teensytheremin/theremin/schematics/ltspice/2023_03_bjt_dual_ota_current_sensing_oscillator_v01.asc

C1: cap; 10pF
C_ant: cap; 8pF
C_hand: cap; 0.0001pF
L1: ind; 2.7mH; Ipk=0.5 Rser=120 Cpar=1.1pF
Q1: npn; 2N3904
Q2: npn; 2N3904
Q3: pnp; 2N3906
Q4: pnp; 2N3906
Q5: npn; 2N3904
Q6: npn; 2N3904
Q7: pnp; 2N3906
Q8: pnp; 2N3906
Q9: npn; 2N3904
Q10: npn; 2N3904
Q11: npn; 2N3904
Q12: npn; 2N3904
R1: res; 180
R2: res; 220
R3: res; 15
R4: res; 2k
R5: res; 47
R6: res; 1
R7: res; 1
R8: res; 100
R9: res; 1.5k
R10: res; 47
R11: res; 1
R_loss: res; 10Meg
V1: voltage; 3.3
Named nets: 0, COM, ANT, DRIVE, SENSE
.tran 0 1000u 10u 1n uic
Current Sensing OTA Based Theremin Oscillator
.ic I(L1)=0.0001
