teensytheremin/theremin/schematics/ltspice/2023_04_bjt_trans_cond_mixer_with_volume_vca_v01.asc

C1: cap; 2.2µF
C2: cap; 1nF
C3: cap; 1nF
C4: cap; 1nF
C5: cap; 360nF
C8: cap; 10nF
Q1: npn; 2N3904
Q2: npn; 2N3904
Q3: npn; 2N3904
Q4: npn; 2N3904
Q5: pnp; 2N3906
Q6: pnp; 2N3906
Q7: npn; 2N3904
Q8: npn; 2N3904
Q9: npn; 2N3904
Q10: npn; 2N3904
Q11: npn; 2N3904
Q12: pnp; 2N3906
Q13: pnp; 2N3906
Q14: npn; 2N3904
R1: res; 220
R2: res; 220
R3: res; 10k
R4: res; 10k
R5: res; 10k
R6: res; 15k
R7: res; 10k
R8: res; 10k
R9: res; 220
R10: res; 470
R11: res; 470
R12: res; 470
R15: res; 2.2k
R16: res; 2.2k
V1: voltage; 3.3
V2: voltage; SINE(1.65 0.5 1000000)
V3: voltage; SINE(1.65 0.8 10)
V5: voltage; SINE(1.65 0.5 1001000)
Named nets: 0, COM, IN1, IN2, OUT, VCTL
.tran 0 307m 3m uic
High Quality Operational Transconductance Amplifier based Theremin Mixer with volume control
1 Vpp
1 Vpp
1 Vpp
Volume voltage control (<0.1.1V to mute)
