teensytheremin/theremin/schematics/ltspice/2023_03_bjt_trans_cond_mixer_v01.asc

C1: cap; 360nF
C2: cap; 1nF
C3: cap; 1nF
C4: cap; 1nF
Q1: npn; 2N3904
Q2: npn; 2N3904
Q3: npn; 2N3904
Q4: npn; 2N3904
Q5: pnp; 2N3906
Q6: pnp; 2N3906
Q7: npn; 2N3904
R1: res; 2.2k
R2: res; 2.2k
R3: res; 10k
R4: res; 10k
R5: res; 10k
R6: res; 15k
R7: res; 10k
R8: res; 10k
R9: res; 220
V1: voltage; 3.3
V2: voltage; SINE(1.65 0.5 1000000)
V5: voltage; SINE(1.65 0.5 1001000)
Named nets: 0, COM, OUT, IN1, IN2
.tran 0 7m 3m uic
High Quality Operational Transconductance Amplifier based Theremin Mixer
1 Vpp
1 Vpp
1 Vpp
