teensytheremin/theremin/schematics/ltspice/2023_03_bjt_trans_cond_volt_follower_current_sensing_buffer_v01.asc

C_ant: cap; 8pF
C_hand: cap; 0.0001pF
I1: current; 6mA
L1: ind; 2.7mH; Ipk=0.5 Rser=120 Cpar=1.1pF
Q1: npn; 2N3904
Q2: npn; 2N3904
Q3: npn; 2N3904
Q4: npn; 2N3904
Q5: npn; 2N3904
Q6: npn; 2N3904
Q7: pnp; 2N3906
Q8: pnp; 2N3906
Q9: npn; 2N3904
Q10: pnp; 2N3906
Q11: pnp; 2N3906
Q12: pnp; 2N3906
R1: res; 470
R2: res; 470
R3: res; 1
R4: res; 1
R5: res; 1
R6: res; 1
R7: res; 1
R8: res; 1
R9: res; 1
R10: res; 1
R11: res; 1.1
R12: res; 1
R_loss: res; 10Meg
V1: voltage; 3.3
V2: voltage; SINE(1.65 0.75 1014288)
Named nets: 0, COM, ANT, DRIVE, SENSE, DRV_IN
.tran 0 230u 200u 1n uic
Current Sensing Theremin 
Analog Frontend
.ic V(ANT)=0.00001
