teensytheremin/theremin/schematics/ltspice/2023_03_bjt_diff_amp_volt_follower_buffer_v01.asc

C_ant: cap; 8pF
C_hand: cap; 0.0001pF
L1: ind; 2.7mH; Ipk=0.5 Rser=120 Cpar=1.1pF
Q1: npn; 2N3904
Q2: npn; 2N3904
Q3: pnp; 2N3906
Q4: pnp; 2N3906
Q5: npn; 2N3904
Q6: npn; 2N3904
Q7: npn; 2N3904
Q8: npn; 2N3904
Q9: npn; 2N3904
R1: res; 22
R2: res; 470
R3: res; 470
R_loss: res; 10Meg
V1: voltage; 3.3
V2: voltage; SINE(1.55 0.85 1014288)
Named nets: 0, COM, ANT, DRIVE, SENSE, DRV_IN
.tran 0 2m 1u 1n uic
Current Sensing Theremin Oscillator
.ic V(ANT)=0.0001
