teensytheremin/theremin/schematics/ltspice/2023_03_wallin_oscillator_bjt_diff_amp_volt_follower_buffer_v01.asc

C11: cap; 2nF
C12: cap; 2nF
C13: cap; 2nF
C_ant: cap; 8pF
C_hand: cap; 0.0001pF
L1: ind; 2.7mH; Ipk=0.5 Rser=120 Cpar=1.1pF
Q11: npn; 2N3904
Q12: npn; 2N3904
Q13: npn; 2N3904
Q15: pnp; 2N3906
Q16: pnp; 2N3906
Q17: npn; 2N3904
Q18: npn; 2N3904
Q19: npn; 2N3904
Q20: npn; 2N3904
Q21: npn; 2N3904
Q22: npn; 2N3904
Q23: npn; 2N3904
Q24: npn; 2N3904
Q25: npn; 2N3904
Q26: npn; 2N3904
Q28: npn; 2N3904
Q29: npn; 2N3904
R3: res; 270k
R7: res; 470
R20: res; 270k
R23: res; 47
R24: res; 510
R25: res; 2k
R29: res; 22
R37: res; 330
R_loss: res; 10Meg
V1: voltage; 3.3
Named nets: 0, COM, ANT, DRIVE, SENSE, SENSE_BUF, DRV_IN, AMP_OUT
.tran 0 2m 1u 1n uic
Current Sensing Theremin Oscillator
.ic V(ANT)=0.0001
