teensytheremin/theremin/schematics/ltspice/2023_03_wallin_oscillator_bjt_power_rails_diff_amp_4bjt_buffer_v01.asc

C1: cap; 1nF
C2: cap; 1nF
C3: cap; 1nF
C4: cap; 1nF
C5: cap; 0.1µF
C6: cap; 0.1µF
C7: cap; 10nF
C8: cap; 0.1µF
C_ant: cap; 8pF
C_hand: cap; 0.0001pF
L1: ind; 2.7mH; Ipk=0.5 Rser=120 Cpar=1.1pF
Q1: npn; 2N3904
Q2: npn; 2N3904
Q3: npn; 2N3904
Q4: npn; 2N3904
Q5: pnp; 2N3906
Q6: pnp; 2N3906
Q7: pnp; 2N3906
Q8: npn; 2N3904
Q9: npn; 2N3904
Q10: pnp; 2N3906
R1: res; 47
R2: res; 47
R3: res; 270
R4: res; 200
R5: res; 200
R6: res; 470
R7: res; 470
R8: res; 15k
R9: res; 15k
R10: res; 1.5k
R11: res; 1k
R_loss: res; 10Meg
V1: voltage; 3.3
Named nets: 0, COM, ANT, Vbias, DRIVE, DOUT, DIN
.tran 0 2m 1u 1n uic
Current Sensing Theremin Oscillator
.ic V(ANT)=0.0001
