teensytheremin/theremin/schematics/ltspice/2023_03_wallin_oscillator_bjt_power_rails_diff_amp_with_current_mirror_v01.asc

C1: cap; 1nF
C2: cap; 1nF
C3: cap; 1nF
C4: cap; 1nF
C5: cap; 0.1µF
C6: cap; 0.1µF
C_ant: cap; 8pF
C_hand: cap; 0.0001pF
L1: ind; 2.7mH; Ipk=0.5 Rser=120 Cpar=1.1pF
Q1: npn; 2N3904
Q2: npn; 2N3904
Q3: npn; 2N3904
Q4: npn; 2N3904
Q5: pnp; 2N3906
Q6: pnp; 2N3906
R1: res; 22
R2: res; 22
R3: res; 22
R4: res; 47
R5: res; 360
R6: res; 24k
R7: res; 24k
R8: res; 1k
R9: res; 1k
R_loss: res; 10Meg
V1: voltage; 3.3
Named nets: 0, COM, ANT
.tran 0 1m 10u 1n uic
Current Sensing Theremin Oscillator
.ic V(ANT)=0.0001
