teensytheremin/theremin/schematics/ltspice/2023_03_wallin_oscillator_bjt_power_rails_diff_amp_v01.asc

C1: cap; 1nF
C2: cap; 1nF
C3: cap; 1nF
C4: cap; 1nF
C5: cap; 0.1µF
C6: cap; 0.1µF
C_ant: cap; 8pF
C_hand: cap; 0.0001pF
L1: ind; 2.7mH; Ipk=0.5 Rser=120 Cpar=1.1pF
Q1: npn; 2N3904
Q2: npn; 2N3904
Q3: npn; 2N3904
Q4: npn; 2N3904
Q5: pnp; 2N3906
Q6: npn; 2N3904
Q7: npn; 2N3904
Q8: pnp; 2N3906
Q10: npn; 2N3904
Q11: npn; 2N3904
R1: res; 33
R2: res; 33
R3: res; 1.2k
R4: res; 860
R5: res; 860
R6: res; 1.5k
R7: res; 1k
R8: res; 1k
R9: res; 1k
R10: res; 47k
R11: res; 47k
R_loss: res; 10Meg
V1: voltage; 3.3
Named nets: 0, COM, ANT, Vbias, VP, VN, DRIVE
.tran 0 2m 10u 1n uic
Current Sensing Theremin Oscillator
.ic V(ANT)=0.0001
