teensytheremin/theremin/schematics/ltspice/2023_02_sine_drive_phase_shift.asc

C2: cap; 100nF
C_ant: cap; 8pF
C_hand: cap; 0.001pF
L1: ind; 2.7mH; Ipk=0.5 Rser=120 Cpar=1.1pF
R1: res; 8.2K
R2: res; 2.2K
R3: res; 22
R7: res; 10K
R_loss: res; 100Meg
U2: adcmp601
U3: adcmp601
U4: ad8651
V1: voltage; 3.3V
V2: voltage; SINE(0.344 0.306 1015.288KHz)
Named nets: 0, COM, DRV065, DRIVE, ANT, SENSE, REF
.tran 0 500u 100u
Air core inductor
Theremin sensor analog frontend
AD9833 sin out
