teensytheremin/theremin/schematics/ltspice/2021_current_sensing_unbuffered_inverters_06.asc

C1: cap; 0.1µF
C2: cap; 47pF
C3: cap; 47pF
C4: cap; 47pF
C_ant: cap; 10pF
L2: ind; 2700µH; Rser=120 Cpar=1.2pF
Q1: pnp; BC857B
Q2: pnp; BC857B
Q3: npn; BC847B
Q4: npn; BC847B
R1: res; 2.2
R2: res; 2.2
R3: res; 10
R4: res; 10
R5: res; 1.5k
R6: res; 1.5k
R7: res; 1.5k
R8: res; 100k
R9: res; 100k
R10: res; 100k
U1: 74LVCU04NXP
U2: 74LVCU04NXP
U3: 74LVCU04NXP
U4: 74LVCU04NXP
V2: voltage; 3.3V
Named nets: 0, COM, SENSE2, ANT, DRIVE, OUT2, SENSE1
.tran 0 5m 0.001u 0.3n
Theremin sensor - current sensing oscillator on 74LVC2GU04 unbuffered inverters and BJT current mirrors
.ic I(L1)=0.001u
Current sensor
Preamp
Driver
Output buffer
