teensytheremin/theremin/schematics/ltspice/2021_current_sensing_unbuffered_inverters_05.asc

C1: cap; 220pF
C2: cap; 220pF
C3: cap; 1µF
C_ant: cap; 10pF
L1: ind; 2700µH; Rser=120 Cpar=1.2pF
R1: res; 10
R2: res; 10
R3: res; 1k
R4: res; 1k
R5: res; 100k
R6: res; 100k
R7: res; 100k
U1: 74LVCU04NXP
U2: 74LVCU04NXP
U3: 74LVCU04NXP
U4: 74LVCU04NXP
V2: voltage; 3.3V
Named nets: 0, COM, ANT, DRIVE, SENSE, OUT, TOPV, BOTTOMV
.tran 0 5m 0.001u 0.3n
Current sensing oscillator on unbuffered inverters
.ic I(L1)=0.001u
