teensytheremin/theremin/schematics/ltspice/2021_current_sensing_unbuffered_inverters_03.asc

C1: cap; 200pF
C2: cap; 200pF
C3: cap; 0.1µF
C_ant: cap; 10pF
L1: ind; 2700µH; Rser=120 Cpar=1.2pF
R1: res; 10
R2: res; 10
R3: res; 100k
R4: res; 100k
U1: 74HCU04X
U2: 74HCU04X
U3: 74HCU04X
U4: 74HCU04X
U5: 74HCU04X
U6: 74HCU04X
V2: voltage; 3.3V
Named nets: 0, COM, ANT, DRIVE, OUT
.tran 0 5m 0.001u 0.1n
Current sensing oscillator on unbuffered inverters
.ic I(L1)=0.001u
