teensytheremin/theremin/schematics/ltspice/2021_current_sensing_unbuffered_inverters_01.asc

C1: cap; 0.1µF
C6: cap; 0.01µF
C_ant1: cap; 8pF
C_ant: cap; 8pF
L1: ind; 2700µH; Rser=120 Cpar=1.2pF
L2: ind; 2700µH; Rser=120 Cpar=1.2pF
R1: res; 1
R2: res; 1
R3: res; 47
R4: res; 220
R5: res; 220
R6: res; 1
R7: res; 22
R8: res; 22
R9: res; 1
R10: res; 15
R11: res; 15
R12: res; 1
R13: res; 47
R14: res; 1000
R15: res; 1045
R16: res; 1
R17: res; 1000k
R19: res; 1000k
U1: SN74LVC2GU04
U2: SN74LVC2GU04
U3: 74HCU04X
U4: SN74LVC2GU04
U5: SN74LVC2GU04
U6: 74HCU04X
U7: 74HCU04X
U8: 74HCU04X
V2: voltage; 3.3V
Named nets: 0, COM, ANT, DRIVE, OUT, ANT2, DRIVE2, OUT2
.tran 0 5m 0.001u 0.1n
.ic I(L1)=0.001u
.ic I(L2)=0.01u
Current sensing oscillator on unbuffered inverters
