teensytheremin/theremin/schematics/ltspice/2021_current_sensing_pll_bjts_01.asc

C1: cap; 1µF
C2: cap; 1µF
C3: cap; 1µF
C4: cap; 1µF
C5: cap; 1µF
C6: cap; 1µF
C7: cap; 470pF
C8: cap; 0.1µF
C9: cap; 100pF
C11: cap; 0.1µF
C_ant: cap; 10pF
C_vco: cap; 160pF
L1: ind; 2700µH; Rser=120 Cpar=1.2pF
L2: ind; 100µH; Rser=120 Cpar=1.2pF
Q1: pnp; 2N3906
Q2: npn; 2N3904
Q3: pnp; 2N3906
Q4: npn; 2N3904
Q5: pnp; 2N3906
Q6: npn; 2N3904
Q7: npn; 2N3904
Q8: pnp; 2N3906
Q9: npn; 2N3904
Q10: pnp; 2N3906
Q11: npn; 2N3904
Q12: pnp; 2N3906
Q13: npn; 2N3904
Q14: pnp; 2N3906
Q15: npn; 2N3904
Q16: pnp; 2N3906
Q17: npn; 2N3904
Q18: pnp; 2N3906
Q19: npn; 2N3904
Q20: pnp; 2N3906
R1: res; 2.2k
R2: res; 2.2k
R3: res; 2
R4: res; 2
R5: res; 1k
R6: res; 1k
R7: res; 10
R8: res; 10
R9: res; 1k
R10: res; 4.7k
R11: res; 470
R12: res; 4.7k
R13: res; 470
R14: res; 10
R15: res; 10
R16: res; 10k
R17: res; 10k
R18: res; 4.7k
R19: res; 220
R20: res; 10k
R23: res; 330
R24: res; 1500
R25: res; 4.7k
R27: res; 4.7k
R28: res; 4.7k
U1: BBY65-02V
U2: BBY65-02V
U3: 74lvc86a
U4: SN74LVC1GX04
U5: SN74LVC1GX04
V2: voltage; 3.3V
Named nets: 0, COM, ANT, DRIVE, DRIVE_IN, VCOINDOUT, VCODRIVE, OUT, SENSE, VCO90, VCOCTL
.tran 0 5m 0.001u 1n
.ic I(L2)=0.0001u
integrator
VCO current sensing
drive current sensing
VCO tank
drive
VCO drive
antenna tank
phase detector
Current Sensing PLL Theremin Oscillator
phase correction
