teensytheremin/theremin/schematics/ltspice/2021_current_sensing_8bjts_01.asc

C1: cap; 1µF
C2: cap; 1µF
C3: cap; 1µF
C_ant: cap; 8pF
D1: diode
D2: diode
L1: ind; 2700µH; Rser=120 Cpar=1.2pF
Q1: pnp; 2N3906
Q2: npn; 2N3904
Q3: pnp; 2N3906
Q4: npn; 2N3904
Q5: pnp; 2N3906
Q6: npn; 2N3904
Q7: npn; 2N3904
Q8: pnp; 2N3906
R1: res; 470
R2: res; 470
R3: res; 2.2
R4: res; 2.2
R5: res; 1k
R6: res; 1k
R7: res; 15
R8: res; 15
R9: res; 470
V2: voltage; 3.3V
Named nets: 0, COM, ANT, DRIVE, SENSE_OUT
.tran 0 5m 0.001u 1n
.ic I(L1)=0.001u
