teensytheremin/theremin/schematics/ltspice/2021_current_sensing_opamps_pll_01.asc

C1: cap; 0.1µ
C2: cap; 0.1µ
C3: cap; 120pF
C4: cap; 220pF
C5: cap; 0.01µ
C6: cap; 330pF
C7: cap; 0.33µ
C8: cap; 33pF
C_ant1: cap; 10pF
L1: ind; 200µH; Rser=3 Cpar=1.2pF
L2: ind; 2700µH; Rser=120 Cpar=1.2pF
R1: res; 220
R2: res; 2.7k
R3: res; 220
R4: res; 2.7k
R5: res; 220
R6: res; 100
R7: res; 220
R8: res; 1k
R9: res; 1.1k
R10: res; 2.2k
R11: res; 1k
R12: res; 3.3k
R13: res; 22k
R14: res; 33k
R15: res; 47
R16: res; 1000
R17: res; 22k
R20: res; 1k
R21: res; 1k
R_sense: res; 10
U1: ad8132
U2: ADA4807-1
U3: adcmp601
U4: 74lvc86a
U6: SN74LVC1GX04
U7: SN74LVC1GX04
U8: AD8541
U100: BBY65-02V
U101: BBY65-02V
V2: voltage; 3.3V
Named nets: 0, COM, VCOINDOUT, VCOINDIN, VCODRIVE, ANT, IND_IN, OUT, DRIVE, VCOCTL
.tran 0 5m 0.001u 5n
.ic I(L1)=0.001u
