teensytheremin/theremin/schematics/ltspice/2021_current_sensing_dual_opamps_01.asc

C2: cap; 330pF
C4: cap; 0.1µ
C_ant: cap; 10pF
L1: ind; 2700µH; Rser=120 Cpar=1.2pF
R1: res; 22k
R4: res; 2.4k
R5: res; 2.4k
R6: res; 110
R7: res; 110
R8: res; 10k
R9: res; 10
R10: res; 1k
R11: res; 3k
U1: ad8132
U2: ADA4807-1
V2: voltage; 3.3V
Named nets: 0, COM, ANT, TANK_IN, DRIVE, DIFF
.tran 0 5m 0.001u 1n
.ic I(L1)=0.001u
