teensytheremin/theremin/schematics/ltspice/2021_current_sensing_unbuffered_inverter_01.asc

C1: cap; 0.1µF
C2: cap; 0.1µF
C3: cap; 0.1µF
C_ant1: cap; 8pF
C_ant2: cap; 8pF
L1: ind; 2700µH; Rser=120 Cpar=1.2pF
L2: ind; 2700µH; Rser=120 Cpar=1.2pF
Q1: npn; 2N3904
Q2: npn; 2N3904
Q3: pnp; 2N3906
Q4: pnp; 2N3906
R1: res; 10
R2: res; 10
R3: res; 470
R4: res; 470
R5: res; 10
R6: res; 10
R7: res; 470
R8: res; 470
R9: res; 2.2k
R10: res; 2.2k
R11: res; 10
R12: res; 10
U3: SN74LVC2GU04
U4: SN74LVC2GU04
U5: SN74LVC2GU04
U6: SN74LVC2GU04
V2: voltage; 3.3V
Named nets: 0, COM, ANT1, ANT2, DRIVE2, DRIVE1
.tran 0 5m 0.001m 0.0001u
.ic I(L1)=0.001u
.ic I(L2)=0.001u
