teensytheremin/theremin/schematics/ltspice/2021_current_sensing_oscillator_lt6200_01.asc

C1: cap; 0.5pF
C2: cap; 0.5pF
C3: cap; 0.1µF
C_ant: cap; 8pF
C_touch: cap; 330pF
D1: diode; BAS216
D2: diode; BAS216
D3: diode
D4: diode
D23: diode; BAS216
D24: diode; BAS216
L1: ind; 2.7mH; Rser=120 Cpar=1.2pF
Q29: npn; 2N3904
Q30: npn; 2N3904
R1: res; 220
R2: res; 220
R3: res; 2200
R4: res; 2200
R5: res; 220
R6: res; 220
R39: res; 10
R42: res; 100
R_sense: res; 22
R_touch: res; 150k
U1: LT6200-10
U2: ad8651
V2: voltage; 3.3V
Named nets: 0, COM, ANT, DRIVE, OUT
.tran 0 5m 0.001m 0.001u
.ic I(L1)=0.0001u
output buffer
ESD protection diodes
Current sensing Theremin oscillator
touch simulation
Limiter
