teensytheremin/theremin/schematics/ltspice/2021_current_sensing_current_mirrors_oscillator_05.asc

C1: cap; 10pF
C2: cap; 10pF
C11: cap; 10pF
D1: diode
D2: diode
D3: diode
D4: diode
L1: ind; 2.7mH; Rser=120 Cpar=1.2pF
L2: ind; 2.7mH; Rser=120 Cpar=1.2pF
L3: ind; 2.7mH; Rser=120 Cpar=1.2pF
Q1: pnp; 2N3906
Q2: pnp; 2N3906
Q3: npn; 2N3904
Q4: npn; 2N3904
Q5: pnp; 2N3906
Q6: pnp; 2N3906
Q7: npn; 2N3904
Q8: npn; 2N3904
Q9: pnp; 2N3906
Q10: npn; 2N3904
Q11: npn; 2N3904
Q12: pnp; 2N3906
R1: res; 3.3k
R2: res; 3.3k
R3: res; 33
R4: res; 33
R5: res; 2200
R6: res; 1000
R7: res; 1000
R8: res; 10
R9: res; 10
R10: res; 10
R11: res; 10
U3: ad8651
V1: voltage; SINE(1.65 1.65 915229)
V2: voltage; 3.3V
V3: voltage; 1.65
V4: voltage; PULSE(0 3.3 0 0.03u 0.03u 0.516311u 1.092623u)
Named nets: 0, COM, VREF, SIN_IN, SQ_IN, ANT, DRIVE, OPAMPOUT
.tran 0 5m 0.001m 0.001u
#.TRAN 1m
#.IC I(L)=6.188u
.IC I(L)=6.19u
.MEAS TRAN t1 V(Vant) WHEN V(Vant) = 0 rise=1
.MEAS TRAN t2 V(Vant) WHEN V(Vant) = 0 rise=2
.MEAS TRAN freq21 PARAM 1/(t2-t1)
.ic I(L3)=0.0001u
