teensytheremin/theremin/schematics/ltspice/2021_pll_current_sensing_04.asc

C1: cap; 100nF
C2: cap; 0.1µF
C3: cap; 1µF
C4: cap; 0.1µF
C5: cap; 0.1µF
C6: cap; 220pF
C7: cap; 0.1µF
C8: cap; 100nF
C9: cap; 0.1µF
C10: cap; 0.1µF
C11: cap; 100nF
C12: cap; 0.1µF
C_ant: cap; 10pF
C_hand: cap; 0.1pF
L1: ind; 2.7mH; Rser=120 Cpar=1.5pF
R1: res; 4.7K
R2: res; 1K
R3: res; 1
R4: res; 1
R5: res; 1
R6: res; 2K
R7: res; 1
R8: res; 680
R9: res; 4.7K
R10: res; 3.3K
R15: res; 1
R16: res; 1
R17: res; 1
R18: res; 22K
R_sense: res; 22
U1: LTC6752
U2: LTC6752
U3: 74lvc74a
U4: ad8651
U5: 74lvc86a
U6: LTC6752
U7: ad8651
V1: voltage; 3.3V; Rser=0.1
V3: voltage; 1.65
Named nets: 0, COM, VREF, ANT, OUT, VCOCTL, DRIVE, PHASE
Current Sensing Theremin Oscillator with PLL
.tran 0 3m 30u 0.001u
